Falrahch/AY-3-8910_Synthesizer_Module/inc/notes.h

#pragma once

#include "mbed.h"

#define NOTETABLEOFFSET 23
// contains decimal representatives of the values that need to be written in the
// tone registers
uint16_t notes[] = {
    3421, // C1
    3228, 3047, 2876, 2715, 2562, 2419, 2283, 2155, 2034, 1920, 1812,
    1710, // C2
    1614, 1524, 1438, 1357, 1281, 1209, 1141, 1077, 1017, 960,  906,
    855, // C3
    807,  762,  719,  679,  641,  605,  571,  539,  508,  480,  453,  428,
    404, // C4
    381,  360,  339,  320,  302,  285,  269,  254,  240,  226,
    214, // C5
    202,  190,  180,  170,  160,  151,  143,  135,  127,  120,  113,
    107, // C6
    101,  95,   90,   85,   80,   76,   71,   67,   64,   60,   57,
    53, // C7
    50,   48,   45,   42,   40,   38,   36,   34,   32,   30,   28,
    27, // C8
    25,   24,   22,   21,   20,   19,   18,   17,   16,   15,   14};
